ivan-ef/avr-transistor-tester/software/ILI9163.h

/* ************************************************************************
 *
 *   ILI9163 color graphic display controller
 *
 *   (c) 2017-2025 by Markus Reschke
 *
 * ************************************************************************ */


/* ************************************************************************
 *   commands
 * ************************************************************************ */


/*
 *  no operation
 *  - 1 byte cmd
 */

#define CMD_NOP               0b00000000     /* no operation */


/*
 *  software reset
 *  - 1 byte cmd
 */

#define CMD_RESET             0b00000001     /* software reset */


/*
 *  read display identification information
 *  - 1 byte cmd + 4 bytes data (read mode)
 */

#define CMD_READ_DISP_ID      0b00000100     /* read display ID */

/* data byte #1: dummy byte */
/* data byte #2: manufacturer ID (0x54) */
/* data byte #3: module/driver version ID (0x80) */
/* data byte #4: module/driver version ID (0x66) */


/*
 *  read display status
 *  - 1 byte cmd + 5 bytes data (read mode)
 */

#define CMD_READ_STATUS       0b00001001     /* read display status */

/* data byte #1: dummy data */

/* data byte #2: status */
  /* horizontal refresh (horizontal order): */
#define FLAG_STAT_HOR_NORM    0b00000000     /* increment, left to right */
#define FLAG_STAT_HOR_REV     0b00000010     /* decrement, right to left */
  /* RGB/BGR order */
#define FLAG_STAT_COLOR_RGB   0b00000000     /* RGB */
#define FLAG_STAT_COLOR_BGR   0b00000100     /* BGR */
  /* vertical refresh (scan address order): */
#define FLAG_STAT_VER_NORM    0b00000000     /* increment, top to bottom */
#define FLAG_STAT_VER_REV     0b00001000     /* decrement, bottom to top */
  /* row/column exchange: */
#define FLAG_STAT_XY_NORM     0b00000000     /* normal */
#define FLAG_STAT_XY_REV      0b00010000     /* reversed (X & Y swapped) */
  /* column address order: */
#define FLAG_STAT_COL_NORM    0b00000000     /* increment, left to right */
#define FLAG_STAT_COL_REV     0b00100000     /* decrement, right to left */
  /* row address order: */
#define FLAG_STAT_ROW_NORM    0b00000000     /* increment, top to bottom */
#define FLAG_STAT_ROW_REV     0b01000000     /* decrement, bottom to top */
  /* booster voltage: */
#define FLAG_STAT_BOOST_OFF   0b00000000     /* booster on */
#define FLAG_STAT_BOOST_ON    0b10000000     /* booster off */

/* data byte #3: status */
  /* display normal mode: */
#define FLAG_STAT_NORM_OFF    0b00000000     /* off */
#define FLAG_STAT_NORM_ON     0b00000001     /* on */
  /* sleep mode: */
#define FLAG_STAT_SLEEP_OFF   0b00000000     /* off */
#define FLAG_STAT_SLEEP_ON    0b00000010     /* on */
  /* partial mode: */
#define FLAG_STAT_PART_OFF    0b00000000     /* off */
#define FLAG_STAT_PART_ON     0b00000100     /* on */
  /* idle mode: */
#define FLAG_STAT_IDLE_OFF    0b00000000     /* off */
#define FLAG_STAT_IDLE_ON     0b00001000     /* on */
  /* interface color pixel format: */
#define FLAG_STAT_PIX_12      0b00110000     /* 12 bits per pixel */
#define FLAG_STAT_PIX_16      0b01010000     /* 16 bits per pixel */
#define FLAG_STAT_PIX_18      0b01100000     /* 18 bits per pixel */

/* data byte #4: status */
  /* gamma curve - bit 2: bit 0 (always 0) */
  /* tearing effect line: */
#define FLAG_STAT_TEAR_OFF    0b00000000     /* off */
#define FLAG_STAT_TEAR_ON     0b00000010     /* on */
  /* display: */
#define FLAG_STAT_DISP_OFF    0b00000000     /* off */
#define FLAG_STAT_DISP_ON     0b00000100     /* on */
  /* inversion: */
#define FLAG_STAT_INV_OFF     0b00000000     /* off */
#define FLAG_STAT_INV_ON      0b00100000     /* on */
  /* vertical scrolling: */
#define FLAG_STAT_VSCROLL_OFF 0b00000000     /* off */
#define FLAG_STAT_VSCROLL_ON  0b10000000     /* on */

/* data byte #5: status */
  /* tearing effect line mode: */
#define FLAG_STAT_TEAR_MODE1  0b00000000     /* mode 1: V-blanking */
#define FLAG_STAT_TEAR_MODE2  0b00100000     /* mode 2: V-blanking and H-blanking */
  /* gamma curve - bits 1 and 0: */
#define FLAG_STAT_GAMMA1      0b00000000     /* gamma curve 1 */
#define FLAG_STAT_GAMMA2      0b01000000     /* gamma curve 2 */
#define FLAG_STAT_GAMMA3      0b10000000     /* gamma curve 3 */
#define FLAG_STAT_GAMMA4      0b11000000     /* gamma curve 4 */


/*
 *  read display power mode
 *  - 1 byte cmd + 2 bytes data (read mode)
 */

#define CMD_READ_PWR_MODE     0b00001010     /* read display power mode */

/* data byte #1: dummy data */

/* data byte #2: status */
  /* display: */
#define FLAG_DISPLAY_OFF      0b00000000     /* off */
#define FLAG_DISPLAY_ON       0b00000100     /* on */
  /* display normal mode: */
#define FLAG_NORMAL_OFF       0b00000000     /* off (partial display) */
#define FLAG_NORMAL_ON        0b00001000     /* on (normal display) */
  /* sleep mode: */
#define FLAG_SLEEP_OFF        0b00000000     /* off (sleep in) */
#define FLAG_SLEEP_ON         0b00010000     /* on (sleep out) */
  /* partial mode: */
#define FLAG_PARTIAL_OFF      0b00000000     /* off */
#define FLAG_PARTIAL_ON       0b00100000     /* on */
  /* idle mode: */
#define FLAG_IDLE_OFF         0b00000000     /* off */
#define FLAG_IDLE_ON          0b01000000     /* on */
  /* booster voltage: */
#define FLAG_BOOSTER_OFF      0b00000000     /* off */
#define FLAG_BOOSTER_ON       0b10000000     /* on */


/*
 *  read display MADCTL (memory access control)
 *  - 1 byte cmd + 2 bytes data (read mode)
 */

#define CMD_READ_MADCTL       0b00001011     /* read display MADCTL */

/* data byte #1: dummy data */

/* data byte #2: status */
/* same as byte #1 of CMD_MEM_CTRL */
  /* horizontal refreshing direction: */
#define RFLAG_HREFRESH_NORM   0b00000000     /* left to right */
#define RFLAG_HREFRESH_REV    0b00000100     /* right to left */
  /* color order: */
#define RFLAG_COLOR_RGB       0b00000000     /* RGB color filter */
#define RFLAG_COLOR_BGR       0b00001000     /* BGR color filter */
  /* vertical refereshing direction: */
#define RFLAG_VREFRESH_NORM   0b00000000     /* top to bottom */
#define RFLAG_VREFRESH_REV    0b00010000     /* bottom to top */
  /* row/column exchange (MCU to memory): */
#define RFLAG_XY_NORM         0b00000000     /* normal */
#define RFLAG_XY_REV          0b00100000     /* reversed (X & Y swapped) */
  /* column address direction (MCU to memory): */
#define RFLAG_COL_NORM        0b00000000     /* left to right */
#define RFLAG_COL_REV         0b01000000     /* right to left */
  /* row address direction (MCU to memory): */
#define RFLAG_ROW_NORM        0b00000000     /* top to bottom */
#define RFLAG_ROW_REV         0b10000000     /* bottom to top */


/*
 *  read display pixel format
 *  - 1 byte cmd + 2 bytes data (read mode)
 */

#define CMD_READ_PIX_FORMAT   0b00001100     /* read display pixel format */

/* data byte #1: dummy data */

/* data byte #2: status */
/* same as byte #1 of CMD_PIX_FORMAT */
  /* MCU interface color format: */
#define RFLAG_IFPF_12         0b00000011     /* 12 bits per pixel */
#define RFLAG_IFPF_16         0b00000101     /* 16 bits per pixel */
#define RFLAG_IFPF_18         0b00000110     /* 18 bits per pixel */


/*
 *  read display image mode
 *  - 1 byte cmd + 2 bytes data (read mode)
 */

#define CMD_READ_IMG_MODE     0b00001101     /* read display image mode */

/* data byte #1: dummy data */

/* data byte #2: status */
  /* gamma curve */
#define FLAG_IMG_GAMMA1       0b00000000     /* gamma curve 1 */
#define FLAG_IMG_GAMMA2       0b00000001     /* gamma curve 2 */
#define FLAG_IMG_GAMMA3       0b00000010     /* gamma curve 3 */
#define FLAG_IMG_GAMMA4       0b00000011     /* gamma curve 4 */
  /* inversion */
#define FLAG_IMG_INV_OFF      0b00000000     /* off */
#define FLAG_IMG_INV_ON       0b00100000     /* on */
  /* vertical scrolling: */
#define FLAG_IMG_VSCROLL_OFF  0b00000000     /* off */
#define FLAG_IMG_VSCROLL_ON   0b10000000     /* on */


/*
 *  read display signal mode
 *  - 1 byte cmd + 2 bytes data (read mode)
 */

#define CMD_READ_SIG_MODE     0b00001110     /* read display signal mode */

/* data byte #1: dummy data */

/* data byte #2: mode flags */
  /* tearing effect line mode: */
#define FLAG_SIG_TEAR_1       0b00000000     /* mode 1 */
#define FLAG_SIG_TEAR_2       0b01000000     /* mode 2 */
  /* tearing effect line: */
#define FLAG_SIG_TEAR_OFF     0b00000000     /* off */
#define FLAG_SIG_TEAR_ON      0b10000000     /* on */


/*
 *  read peripheral self-diagnostic result
 *  - 1 byte cmd + 2 bytes data (read mode)
 */

#define CMD_READ_SELFDIAG     0b00001111     /* read self-diagnostic result */

/* data byte #1: dummy data */

/* data byte #2: flags */
#define FLAG_SELFDIAG_FUNC    0b01000000     /* functionality detection */
#define FLAG_SELFDIAG_REGLOAD 0b10000000     /* register loading detection */


/*
 *  enter sleep mode (sleep in)
 *  - 1 byte cmd
 *  - requires 5ms delay before sending next command
 *  - requires 120ms delay after CMD_SLEEP_OUT
 */

#define CMD_SLEEP_IN          0b00010000     /* enter sleep mode */


/*
 *  leave sleep mode (sleep out)
 *  - 1 byte cmd
 *  - requires 5ms delay before sending next command
 *  - requires 120ms delay after CMD_SLEEP_IN
 */

#define CMD_SLEEP_OUT         0b00010001     /* leave sleep mode */


/*
 *  enter partial display mode
 *  - 1 byte cmd
 */

#define CMD_PARTIAL_MODE      0b00010010     /* enter partial mode */


/*
 *  enter normal display mode
 *  - 1 byte cmd
 */

#define CMD_NORMAL_MODE       0b00010011     /* normal mode on */


/*
 *  disable display inversion
 *  - 1 byte cmd
 */

#define CMD_INVERSION_OFF     0b00100000     /* display inversion off */


/*
 *  enable display inversion (invert pixels)
 *  - 1 byte cmd
 */

#define CMD_INVERSION_ON      0b00100001     /* display inversion on */


/*
 *  select gamma curve
 *  - 1 byte cmd + 1 byte data
 */

#define CMD_GAMMA_SET         0b00100110     /* gamma set */

/* data byte #1: gamma curve */
#define FLAG_GC_1             0b00000001     /* gamma curve 1 */
#define FLAG_GC_2             0b00000010     /* gamma curve 2 */
#define FLAG_GC_3             0b00000100     /* gamma curve 3 */
#define FLAG_GC_4             0b00001000     /* gamma curve 4 */


/*
 *  disable display output
 *  - 1 byte cmd
 */

#define CMD_DISPLAY_OFF       0b00101000     /* display off */


/*
 *  enable display output
 *  - 1 byte cmd
 */

#define CMD_DISPLAY_ON        0b00101001     /* display on */


/*
 *  set column address (accessible frame area)
 *  - 1 byte cmd + 4 bytes data
 */

#define CMD_COL_ADDR_SET      0b00101010     /* set column address */

/* data byte #1: start column - MSB (bits 15-8) */
/* data byte #2: start column - LSB (bits 7-0) */
/* data byte #3: end column - MSB (bits 15-8) */
/* data byte #4: end column - LSB (bits 7-0) */
/* valid range: 0x0000 - 0x007f/0x007f (128x128) */
/*              0x0000 - 0x007f/0x009f (128x160) */
/*              0x0000 - 0x0083/0x00a1 (132x162) */


/*
 *  set row address (accessible frame area)
 *  - 1 byte cmd + 4 bytes data
 */

#define CMD_ROW_ADDR_SET      0b00101011     /* set row address */

/* data byte #1: start row - MSB (bits 15-8) */
/* data byte #2: start row - LSB (bits 7-0) */
/* data byte #3: end row - MSB (bits 15-8) */
/* data byte #4: end row - LSB (bits 7-0) */
/* valid range: 0x0000 - 0x007f/0x007f (128x128) */
/*              0x0000 - 0x009f/0x007f (128x160) */
/*              0x0000 - 0x00a1/0x0083 (132x162) */


/*
 *  write memory (starting at start column and start row)
 *  - 1 byte cmd + x bytes data
 */

#define CMD_MEM_WRITE         0b00101100     /* write memory */

/* data byte #1 - #x: image data */


/*
 *  color setting for 4k, 65k & 262k
 *  - 1 byte cmd + 128 bytes data
 */

#define CMD_COLOR_LUT         0b00101101     /* set color look up table */

/* data byte #1 - #128: look up table data */


/*
 *  read memory (starting at start column and start row)
 *  - 1 byte cmd + x bytes data (read mode)
 */

#define CMD_MEM_READ          0b00101110     /* read memory */

/* data byte #1: dummy data */
/* data byte #2 - #x: image data */


/*
 *  partial area
 *  - 1 byte cmd + 4 bytes data
 */

#define CMD_PARTIAL_AREA      0b00110000     /* set partial area */

/* data byte #1: start row - MSB (bits 15-8) */
/* data byte #2: start row - LSB (bits 7-0) */
/* data byte #3: end row - MSB (bits 15-8) */
/* data byte #4: end row - LSB (bits 7-0) */
/* valid range: 0x0000 - 0x09f/0x00a1 */


/*
 *  vertical scrolling definition (scrolling area)
 *  - 1 byte cmd + 6 bytes data
 */

#define CMD_VSCROLL_AREA      0b00110011     /* set v-scroll area */

/* data byte #1: top fixed area - MSB (bits 15-8) */
/* data byte #2: top fixed area - LSB (bits 7-0) */
/* data byte #3: vertical scrolling area - MSB (bits 15-8) */
/* data byte #4: vertical scrolling area - LSB (bits 7-0) */
/* data byte #5: bottom fixed area - MSB (bits 15-8) */
/* data byte #6: bottom fixed area - LSB (bits 7-0) */


/*
 *  disable tearing effect line
 *  - 1 byte cmd
 */

#define CMD_TEAR_OFF          0b00110100     /* disable tearing effect */


/*
 *  enable tearing effect line
 *  - 1 byte cmd + 1 byte data
 */

#define CMD_TEAR_ON           0b00110101     /* enable tearing effect */

/* data byte #1: mode */
  /* tearing effect mode: */
#define FLAG_TEAR_MODE_0      0b00000000     /* V-blanking only */
#define FLAG_TEAR_MODE_1      0b00000001     /* V-blanking and H-blanking */


/*
 *  memory access control
 *  - 1 byte cmd + 1 byte data
 */

#define CMD_MEM_CTRL          0b00110110     /* memory access control */

/* data byte #1: read/write scanning direction of frame memory */
/* same as byte #2 of CMD_READ_MADCTL */
  /* horizontal refreshing direction: */
#define FLAG_HREFRESH_NORM    0b00000000     /* left to right */
#define FLAG_HREFRESH_REV     0b00000100     /* right to left */
  /* color order: */
#define FLAG_COLOR_RGB        0b00000000     /* RGB color filter */
#define FLAG_COLOR_BGR        0b00001000     /* BGR color filter */
  /* vertical refereshing direction: */
#define FLAG_VREFRESH_NORM    0b00000000     /* top to bottom */
#define FLAG_VREFRESH_REV     0b00010000     /* bottom to top */
  /* row/column exchange (MCU to memory): */
#define FLAG_XY_NORM          0b00000000     /* normal */
#define FLAG_XY_REV           0b00100000     /* reversed (X & Y swapped) */
  /* column address direction (MCU to memory): */
#define FLAG_COL_NORM         0b00000000     /* left to right */
#define FLAG_COL_REV          0b01000000     /* right to left */
  /* row address direction (MCU to memory): */
#define FLAG_ROW_NORM         0b00000000     /* top to bottom */
#define FLAG_ROW_REV          0b10000000     /* bottom to top */


/*
 *  vertical scrolling start address
 *  - 1 byte cmd + 2 bytes data
 */

#define CMD_VSCROLL_START     0b00110111     /* set v-scroll start */

/* data byte #1: start row - MSB (bits 15-8) */
/* data byte #2: start row - LSB (bits 7-0) */


/*
 *  leave idle mode (full color depth)
 *  - 1 byte cmd
 */

#define CMD_IDLE_OFF          0b00111000     /* disable idle mode */


/*
 *  enter idle mode (8bit color depth)
 *  - 1 byte cmd
 */

#define CMD_IDLE_ON           0b00111001     /* enable idle mode */


/*
 *  set pixel format for RGB image data
 *  - 1 byte cmd + 1 byte data
 */

#define CMD_PIX_FORMAT        0b00111010     /* set pixel format */

/* data byte #1: formats */
/* same as byte #2 of CMD_READ_PIX_FORMAT */
  /* MCU interface color format: */
#define FLAG_IFPF_12          0b00000011     /* 12 bits per pixel */
#define FLAG_IFPF_16          0b00000101     /* 16 bits per pixel */
#define FLAG_IFPF_18          0b00000110     /* 18 bits per pixel */


/*
 *  read ID1
 *  - 1 byte cmd + 2 bytes data (read mode)
 */

#define CMD_READ_ID1          0b11011010     /* read ID1 (manufacturer) */

/* data byte #1: dummy data */
/* data byte #2: LCD module manufacturer ID */


/*
 *  read ID2
 *  - 1 byte cmd + 2 bytes data (read mode)
 */

#define CMD_READ_ID2          0b11011011     /* read ID2 (driver version) */

/* data byte #1: dummy data */
/* data byte #2: LCD module/driver version */


/*
 *  read ID3
 *  - 1 byte cmd + 2 bytes data (read mode)
 */

#define CMD_READ_ID3          0b11011100     /* read ID3 (driver) */

/* data byte #1: dummy data */
/* data byte #2: LCD module/driver ID */


/*
 *  frame rate control in normal mode (full color)
 *  - 1 byte cmd + 2 bytes data
 */

#define CMD_FRAME_CTRL_NORM   0b10110001     /* frame control in normal mode */

/* data byte #1: division ratio for internal clock */
  /* valid range: 0 - 15 */

/* data byte #2: v-sync porch for internal clock */
  /* valid range: 0 - 63 */


/*
 *  frame rate control in idle mode (8bit color depth)
 *  - 1 byte cmd + 2 bytes data
 */

#define CMD_FRAME_CTRL_IDLE   0b10110010     /* frame control in idle mode */

/* data byte #1: division ratio for internal clock */
  /* valid range: 0 - 15 */

/* data byte #2: v-sync porch for internal clock */
  /* valid range: 0 - 63 */


/*
 *  frame rate control in partial mode (full color)
 *  - 1 byte cmd + 2 bytes data
 */

#define CMD_FRAME_CTRL_PART   0b10110011     /* frame control in partial mode */

/* data byte #1: division ratio for internal clock */
  /* valid range: 0 - 15 */

/* data byte #2: v-sync porch for internal clock */
  /* valid range: 0 - 63 */



/*
 *  display inversion control
 *  - 1 byte cmd + 1 byte data
 */

#define CMD_INVERS_CTRL       0b10110100     /* display inversion control */

/* data byte #1: mode switches */
  /* for full color partial mode: */
#define FLAG_NLC_LINE         0b00000000     /* line inversion */
#define FLAG_NLC_FRAME        0b00000001     /* frame inversion */
  /* for idle mode: */
#define FLAG_NLB_LINE         0b00000000     /* line inversion */
#define FLAG_NLB_FRAME        0b00000010     /* frame inversion */
  /* for full color normal mode: */
#define FLAG_NLA_LINE         0b00000000     /* line inversion */
#define FLAG_NLA_FRAME        0b00000100     /* frame inversion */


/*
 *  source driver direction control
 *  - 1 byte cmd + 1 byte data
 */

#define CMD_SOURCE_DRV        0b10110111     /* set source driver direction */

/* data byte #1: soure output direction select register */
#define FLAG_SOURCE_DRV_NORM  0b00000000     /* normal */
#define FLAG_SOURCE_DRV_REV   0b00000001     /* reversed */


/*
 *  gate driver direction control
 *  - 1 byte cmd + 1 byte data
 */

#define CMD_GATE_DRV          0b10111000     /* set gate driver direction */

/* data byte #1: source output direction select register */
#define FLAG_GATEE_DRV_NORM   0b00000000     /* normal */
#define FLAG_GATEE_DRV_REV    0b00000001     /* reversed */


/*
 *  power control 1
 *  - 1 byte cmd + 2 bytes data
 */

#define CMD_POWER_CTRL_1      0b11000000     /* power control 1 */

/* data byte #1: GVDD level (reference for VCOM) */
#define FLAG_VRH_500          0b00000000     /* 5.00V */
#define FLAG_VRH_475          0b00000001     /* 4.75V */
#define FLAG_VRH_470          0b00000010     /* 4.70V */
#define FLAG_VRH_465          0b00000011     /* 4.65V */
#define FLAG_VRH_460          0b00000100     /* 4.60V */
#define FLAG_VRH_455          0b00000101     /* 4.55V */
#define FLAG_VRH_450          0b00000110     /* 4.50V */
#define FLAG_VRH_445          0b00000111     /* 4.45V */
#define FLAG_VRH_440          0b00001000     /* 4.40V */
#define FLAG_VRH_435          0b00001001     /* 4.35V */
#define FLAG_VRH_430          0b00001010     /* 4.30V */
#define FLAG_VRH_425          0b00001011     /* 4.25V */
#define FLAG_VRH_420          0b00001100     /* 4.20V */
#define FLAG_VRH_415          0b00001101     /* 4.15V */
#define FLAG_VRH_410          0b00001110     /* 4.10V */
#define FLAG_VRH_405          0b00001111     /* 4.05V */
#define FLAG_VRH_400          0b00010000     /* 4.00V */
#define FLAG_VRH_395          0b00010001     /* 3.95V */
#define FLAG_VRH_390          0b00010010     /* 3.90V */
#define FLAG_VRH_385          0b00010011     /* 3.85V */
#define FLAG_VRH_380          0b00010100     /* 3.80V */
#define FLAG_VRH_375          0b00010101     /* 3.75V */
#define FLAG_VRH_370          0b00010110     /* 3.70V */
#define FLAG_VRH_365          0b00010111     /* 3.65V */
#define FLAG_VRH_360          0b00011000     /* 3.60V */
#define FLAG_VRH_355          0b00011001     /* 3.55V */
#define FLAG_VRH_350          0b00011010     /* 3.50V */
#define FLAG_VRH_345          0b00011011     /* 3.45V */
#define FLAG_VRH_340          0b00011100     /* 3.40V */
#define FLAG_VRH_335          0b00011101     /* 3.35V */
#define FLAG_VRH_325          0b00011110     /* 3.25V */
#define FLAG_VRH_300          0b00011111     /* 3.00V */

/* data byte #2: VCI 1 */
#define FLAG_VCI_275          0b00000000     /* 2.75V */
#define FLAG_VCI_270          0b00000001     /* 2.70V */
#define FLAG_VCI_265          0b00000010     /* 2.65V */
#define FLAG_VCI_260          0b00000011     /* 2.60V */
#define FLAG_VCI_255          0b00000100     /* 2.55V */
#define FLAG_VCI_250          0b00000101     /* 2.50V */
#define FLAG_VCI_245          0b00000110     /* 2.45V */
#define FLAG_VCI_240          0b00000111     /* 2.40V */


/*
 *  power control 2
 *  - 1 byte cmd + 1 byte data
 */

#define CMD_POWER_CTRL_2      0b11000001     /* power control 2 */

/* data byte #1: VGH and VGL factors for step-up converter */
                                             /* VGH / VGL */
#define FLAG_BT_0             0b00000000     /* 4* (9.8)   / -3* (-7.35) */
#define FLAG_BT_1             0b00000001     /* 4* (9.8)   / -4* (-9.8) */
#define FLAG_BT_2             0b00000010     /* 5* (12.25) / -3* (-7.35) */
#define FLAG_BT_3             0b00000011     /* 5* (12.25) / -4* (-9.8) */
#define FLAG_BT_4             0b00000100     /* 5* (12.25) / -5* (-12.25) */
#define FLAG_BT_5             0b00000101     /* 6* (14.7)  / -3* (-7.35) */
#define FLAG_BT_6             0b00000101     /* 6* (14.7)  / -4* (-9.8) */
#define FLAG_BT_7             0b00000111     /* 6* (14.7)  / -5* (-12.25) */


/*
 *  power control 3 (normal mode / full color)
 *  - 1 byte cmd + 2 bytes data
 */

#define CMD_POWER_CTRL_3      0b11000010     /* power control 3 */

/* data byte #1: current for source driver OPamp */
#define FLAG_APA_0            0b00000000     /* least */
#define FLAG_APA_1            0b00000001     /* small */
#define FLAG_APA_2            0b00000010     /* medium low */
#define FLAG_APA_3            0b00000011     /* medium */
#define FLAG_APA_4            0b00000100     /* medium high */
#define FLAG_APA_5            0b00000101     /* large */
#define FLAG_APA_6            0b00000110     /* reserved */
#define FLAG_APA_7            0b00000111     /* reserved */

/* data byte #2: step-up cycles of booster circuit */
                                             /* circuit 1 / circuits 2 & 3 */
#define FLAG_DCA_0            0b00000000     /* BCLK/1 / BCLK/4 */
#define FLAG_DCA_1            0b00000001     /* BCLK/1 / BCLK/8 */
#define FLAG_DCA_2            0b00000010     /* BCLK/1 / BCLK/8 */
#define FLAG_DCA_3            0b00000011     /* BCLK/2 / BCLK/16 */
#define FLAG_DCA_4            0b00000100     /* BCLK/2 / BCLK/16 */
#define FLAG_DCA_5            0b00000101     /* BCLK/4 / BCLK/32 */
#define FLAG_DCA_6            0b00000110     /* BCLK/4 / BCLK/64 */
#define FLAG_DCA_7            0b00000111     /* BCLK/8 / BCLK/64 */


/*
 *  power control 4 (idle mode / 8bit color)
 *  - 1 byte cmd + 2 bytes data
 */

#define CMD_POWER_CTRL_4      0b11000011     /* power control 4 */

/* data byte #1: current for source driver OPamp */
#define FLAG_APB_0            0b00000000     /* least */
#define FLAG_APB_1            0b00000001     /* small */
#define FLAG_APB_2            0b00000010     /* medium low */
#define FLAG_APB_3            0b00000011     /* medium */
#define FLAG_APB_4            0b00000100     /* medium high */
#define FLAG_APB_5            0b00000101     /* large */
#define FLAG_APB_6            0b00000110     /* reserved */
#define FLAG_APB_7            0b00000111     /* reserved */

/* data byte #2: step-up cycles of booster circuit */
                                             /* circuit 1 / circuits 2 & 3 */
#define FLAG_DCB_0            0b00000000     /* BCLK/1 / BCLK/4 */
#define FLAG_DCB_1            0b00000001     /* BCLK/1 / BCLK/8 */
#define FLAG_DCB_2            0b00000010     /* BCLK/1 / BCLK/8 */
#define FLAG_DCB_3            0b00000011     /* BCLK/2 / BCLK/16 */
#define FLAG_DCB_4            0b00000100     /* BCLK/2 / BCLK/16 */
#define FLAG_DCB_5            0b00000101     /* BCLK/4 / BCLK/32 */
#define FLAG_DCB_6            0b00000110     /* BCLK/4 / BCLK/64 */
#define FLAG_DCB_7            0b00000111     /* BCLK/8 / BCLK/64 */


/*
 *  power control 5 (partial mode / full color)
 *  - 1 byte cmd + 2 bytes data
 */

#define CMD_POWER_CTRL_5      0b11000100     /* power control 5 */

/* data byte #1: current for source driver OPamp */
#define FLAG_APC_0            0b00000000     /* least */
#define FLAG_APC_1            0b00000001     /* small */
#define FLAG_APC_2            0b00000010     /* medium low */
#define FLAG_APC_3            0b00000011     /* medium */
#define FLAG_APC_4            0b00000100     /* medium high */
#define FLAG_APC_5            0b00000101     /* large */
#define FLAG_APC_6            0b00000110     /* reserved */
#define FLAG_APC_7            0b00000111     /* reserved */

/* data byte #2: step-up cycles of booster circuit */
                                             /* circuit 1 / circuits 2 & 3 */
#define FLAG_DCC_0            0b00000000     /* BCLK/1 / BCLK/4 */
#define FLAG_DCC_1            0b00000001     /* BCLK/1 / BCLK/8 */
#define FLAG_DCC_2            0b00000010     /* BCLK/1 / BCLK/8 */
#define FLAG_DCC_3            0b00000011     /* BCLK/2 / BCLK/16 */
#define FLAG_DCC_4            0b00000100     /* BCLK/2 / BCLK/16 */
#define FLAG_DCC_5            0b00000101     /* BCLK/4 / BCLK/32 */
#define FLAG_DCC_6            0b00000110     /* BCLK/4 / BCLK/64 */
#define FLAG_DCC_7            0b00000111     /* BCLK/8 / BCLK/64 */


/*
 *  VCOM control 1
 *  - 1 byte cmd + 2 bytes data
 */

#define CMD_VCOM_CTRL_1       0b11000101     /* VCOM control 1 */

/* data byte #1: VCOMH voltage */
#define FLAG_VMH_MIN          0b00000000     /* minumum value */
#define FLAG_VMH_2500         0b00000000     /* 2.500V */
#define FLAG_VMH_2525         0b00000001     /* 2.525V */
#define FLAG_VMH_2550         0b00000010     /* 2.550V */
#define FLAG_VMH_2575         0b00000011     /* 2.575V */
#define FLAG_VMH_2600         0b00000100     /* 2.600V */
#define FLAG_VMH_2625         0b00000101     /* 2.625V */
#define FLAG_VMH_2650         0b00000110     /* 2.650V */
#define FLAG_VMH_2675         0b00000111     /* 2.675V */
#define FLAG_VMH_2700         0b00001000     /* 2.700V */
#define FLAG_VMH_2725         0b00001001     /* 2.725V */
#define FLAG_VMH_2750         0b00001010     /* 2.750V */
#define FLAG_VMH_2775         0b00001011     /* 2.775V */
#define FLAG_VMH_2800         0b00001100     /* 2.800V */
#define FLAG_VMH_2825         0b00001101     /* 2.825V */
#define FLAG_VMH_2850         0b00001110     /* 2.850V */
#define FLAG_VMH_2875         0b00001111     /* 2.875V */
#define FLAG_VMH_2900         0b00010000     /* 2.900V */
#define FLAG_VMH_2925         0b00010001     /* 2.925V */
#define FLAG_VMH_2950         0b00010010     /* 2.950V */
#define FLAG_VMH_2975         0b00010011     /* 2.975V */
#define FLAG_VMH_3000         0b00010100     /* 3.000V */
#define FLAG_VMH_3025         0b00010101     /* 3.025V */
#define FLAG_VMH_3050         0b00010110     /* 3.050V */
#define FLAG_VMH_3075         0b00010111     /* 3.075V */
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
#define FLAG_VML_0175         0b01011101     /* -0.175V */
#define FLAG_VML_0150         0b01011110     /* -0.150V */
#define FLAG_VML_0125         0b01011111     /* -0.125V */
#define FLAG_VML_0100         0b01100000     /* -0.100V */
#define FLAG_VML_0075         0b01100001     /* -0.075V */
#define FLAG_VML_0050         0b01100010     /* -0.050V */
#define FLAG_VML_0025         0b01100011     /* -0.025V */
#define FLAG_VML_0000         0b01100100     /* 0.000V */
#define FLAG_VML_MAX          0b01100100     /* maximum value */


/*
 *  VCOM control 2
 *  - 1 byte cmd + 1 byte data
 */

#define CMD_VCOM_CTRL_2       0b11000110     /* VCOM control 2 */

/* data byte #1: VCOMAC voltage */
 /* range: 0 - 31 */


/*
 *  VCOM offset control
 *  - 1 byte cmd + 1 byte data
 */

#define CMD_VCOM_OFFSET       0b11000111     /* VCOM offset control */

/* data byte #1: */
 /* VCOMH voltage */
                                             /* VMH / VML */
#define FLAG_VMF_MIN          0b00000000     /* minumum value */
#define FLAG_VMF_M64          0b00000000     /* -0 */
#define FLAG_VMF_M63          0b00000001     /* -63d */
#define FLAG_VMF_M62          0b00000010     /* -62d */
#define FLAG_VMF_M61          0b00000011     /* -61d */
#define FLAG_VMF_M60          0b00000100     /* -60d */
#define FLAG_VMF_M59          0b00000101     /* -59d */
#define FLAG_VMF_M58          0b00000110     /* -58d */
#define FLAG_VMF_M57          0b00000111     /* -57d */
#define FLAG_VMF_M56          0b00001000     /* -56d */
#define FLAG_VMF_M55          0b00001001     /* -55d */
#define FLAG_VMF_M54          0b00001010     /* -54d */
#define FLAG_VMF_M53          0b00001011     /* -53d */
#define FLAG_VMF_M52          0b00001100     /* -52d */
#define FLAG_VMF_M51          0b00001101     /* -51d */
#define FLAG_VMF_M50          0b00001110     /* -50d */
#define FLAG_VMF_M49          0b00001111     /* -49d */
#define FLAG_VMF_M48          0b00010000     /* -48d */
#define FLAG_VMF_M47          0b00010001     /* -47d */
#define FLAG_VMF_M46          0b00010010     /* -46d */
#define FLAG_VMF_M45          0b00010011     /* -45d */
#define FLAG_VMF_M44          0b00010100     /* -44d */
#define FLAG_VMF_M43          0b00010101     /* -43d */
#define FLAG_VMF_M42          0b00010110     /* -42d */
#define FLAG_VMF_M41          0b00010111     /* -41d */
#define FLAG_VMF_M40          0b00011000     /* -40d */
#define FLAG_VMF_M39          0b00011001     /* -39d */
#define FLAG_VMF_M38          0b00011010     /* -38d */
#define FLAG_VMF_M37          0b00011011     /* -37d */
#define FLAG_VMF_M36          0b00011100     /* -36d */
#define FLAG_VMF_M35          0b00011101     /* -35d */
#define FLAG_VMF_M34          0b00011110     /* -34d */
#define FLAG_VMF_M33          0b00011111     /* -33d */
#define FLAG_VMF_M32          0b00100000     /* -32d */
#define FLAG_VMF_M31          0b00100001     /* -31d */
#define FLAG_VMF_M30          0b00100010     /* -30d */
#define FLAG_VMF_M29          0b00100011     /* -29d */
#define FLAG_VMF_M28          0b00100100     /* -28d */
#define FLAG_VMF_M27          0b00100101     /* -27d */
#define FLAG_VMF_M26          0b00100110     /* -26d */
#define FLAG_VMF_M25          0b00100111     /* -25d */
#define FLAG_VMF_M24          0b00101000     /* -24d */
#define FLAG_VMF_M23          0b00101001     /* -23d */
#define FLAG_VMF_M22          0b00101010     /* -22d */
#define FLAG_VMF_M21          0b00101011     /* -21d */
#define FLAG_VMF_M20          0b00101100     /* -20d */
#define FLAG_VMF_M19          0b00101101     /* -19d */
#define FLAG_VMF_M18          0b00101110     /* -18d */
#define FLAG_VMF_M17          0b00101111     /* -17d */
#define FLAG_VMF_M16          0b00110000     /* -16d */
#define FLAG_VMF_M15          0b00110001     /* -15d */
#define FLAG_VMF_M14          0b00110010     /* -14d */
#define FLAG_VMF_M13          0b00110011     /* -13d */
#define FLAG_VMF_M12          0b00110100     /* -12d */
#define FLAG_VMF_M11          0b00110101     /* -11d */
#define FLAG_VMF_M10          0b00110110     /* -10d */
#define FLAG_VMF_M09          0b00110111     /* -9d */
#define FLAG_VMF_M08          0b00111000     /* -8d */
#define FLAG_VMF_M07          0b00111001     /* -7d */
#define FLAG_VMF_M06          0b00111010     /* -6d */
#define FLAG_VMF_M05          0b00111011     /* -5d */
#define FLAG_VMF_M04          0b00111100     /* -4d */
#define FLAG_VMF_M03          0b00111101     /* -3d */
#define FLAG_VMF_M02          0b00111110     /* -2d */
#define FLAG_VMF_M01          0b00111111     /* -1d */
#define FLAG_VMF_M00          0b01000000     /* -0 */
#define FLAG_VMF_P00          0b01000000     /* +0 */
#define FLAG_VMF_P01          0b01000001     /* +1d */
#define FLAG_VMF_P02          0b01000010     /* +2d */
#define FLAG_VMF_P03          0b01000011     /* +3d */
#define FLAG_VMF_P04          0b01000100     /* +4d */
#define FLAG_VMF_P05          0b01000101     /* +5d */
#define FLAG_VMF_P06          0b01000110     /* +6d */
#define FLAG_VMF_P07          0b01000111     /* +7d */
#define FLAG_VMF_P08          0b01001000     /* +8d */
#define FLAG_VMF_P09          0b01001001     /* +9d */
#define FLAG_VMF_P10          0b01001010     /* +10d */
#define FLAG_VMF_P11          0b01001011     /* +11d */
#define FLAG_VMF_P12          0b01001100     /* +12d */
#define FLAG_VMF_P13          0b01001101     /* +13d */
#define FLAG_VMF_P14          0b01001110     /* +14d */
#define FLAG_VMF_P15          0b01001111     /* +15d */
#define FLAG_VMF_P16          0b01010000     /* +16d */
#define FLAG_VMF_P17          0b01010001     /* +17d */
#define FLAG_VMF_P18          0b01010010     /* +18d */
#define FLAG_VMF_P19          0b01010011     /* +19d */
#define FLAG_VMF_P20          0b01010100     /* +20d */
#define FLAG_VMF_P21          0b01010101     /* +21d */
#define FLAG_VMF_P22          0b01010110     /* +22d */
#define FLAG_VMF_P23          0b01010111     /* +23d */
#define FLAG_VMF_P24          0b01011000     /* +24d */
#define FLAG_VMF_P25          0b01011001     /* +25d */
#define FLAG_VMF_P26          0b01011010     /* +26d */
#define FLAG_VMF_P27          0b01011011     /* +27d */
#define FLAG_VMF_P28          0b01011100     /* +28d */
#define FLAG_VMF_P29          0b01011101     /* +29d */
#define FLAG_VMF_P30          0b01011110     /* +30d */
#define FLAG_VMF_P31          0b01011111     /* +31d */
#define FLAG_VMF_P32          0b01100000     /* +32d */
#define FLAG_VMF_P33          0b01100001     /* +33d */
#define FLAG_VMF_P34          0b01100010     /* +34d */
#define FLAG_VMF_P35          0b01100011     /* +35d */
#define FLAG_VMF_P36          0b01100100     /* +36d */
#define FLAG_VMF_P37          0b01100101     /* +37d */
#define FLAG_VMF_P38          0b01100110     /* +38d */
#define FLAG_VMF_P39          0b01100111     /* +39d */
#define FLAG_VMF_P40          0b01101000     /* +40d */
#define FLAG_VMF_P41          0b01101001     /* +41d */
#define FLAG_VMF_P42          0b01101010     /* +42d */
#define FLAG_VMF_P43          0b01101011     /* +43d */
#define FLAG_VMF_P44          0b01101100     /* +44d */
#define FLAG_VMF_P45          0b01101101     /* +45d */
#define FLAG_VMF_P46          0b01101110     /* +46d */
#define FLAG_VMF_P47          0b01101111     /* +47d */
#define FLAG_VMF_P48          0b01110000     /* +48d */
#define FLAG_VMF_P49          0b01110001     /* +49d */
#define FLAG_VMF_P50          0b01110010     /* +50d */
#define FLAG_VMF_P51          0b01110011     /* +51d */
#define FLAG_VMF_P52          0b01110100     /* +52d */
#define FLAG_VMF_P53          0b01110101     /* +53d */
#define FLAG_VMF_P54          0b01110110     /* +54d */
#define FLAG_VMF_P55          0b01110111     /* +55d */
#define FLAG_VMF_P56          0b01111000     /* +56d */
#define FLAG_VMF_P57          0b01111001     /* +57d */
#define FLAG_VMF_P58          0b01111010     /* +58d */
#define FLAG_VMF_P59          0b01111011     /* +59d */
#define FLAG_VMF_P60          0b01111100     /* +60d */
#define FLAG_VMF_P61          0b01111101     /* +6d */
#define FLAG_VMF_P62          0b01111110     /* +6d */
#define FLAG_VMF_P63          0b01111111     /* +63d */
#define FLAG_VMF_MAX          0b01111111     /* maximum value */
 /* select VMF value */
#define FLAG_VMF_NV           0b00000000     /* from NV memory */
#define FLAG_VMF_REG          0b10000000     /* from register */


/*
 *  write ID4 value to EEPROM
 *  - 1 byte cmd + 5 bytes data
 */

#define CMD_WRITE_ID4         0b11010011     /* write ID4 */

/* data byte #1: dummy byte */
/* data byte #2: driver IC ID (8 bits) */
/* data byte #3: driver IC part number ID (8 bits) */
/* data byte #4: driver IC version ID (4 bits) */
/* data byte #5: dummy byte */


/*
 *  NV memory function controller
 *  - 1 byte cmd + 3 bytes data
 */

#define CMD_NV_CTRL1          0b11011010     /* NV memory function controller */
// or 0x7d = 0b11010111?

/* data byte #1: fixed value */
#define FLAG_NV_CTRL1_1       0b01010101     /* fixed value 0x55 */

/* data byte #2: fixed value */
#define FLAG_NV_CTRL1_2       0b10101010     /* fixed value 0xaa */

/* data byte #3: fixed value */
#define FLAG_NV_CTRL1_3       0b01100110     /* fixed value 0x66 */


/*
 *  NV memory function controller 2
 *  - 1 byte cmd + 3 bytes data
 */

#define CMD_NV_CTRL2          0b11011010     /* NV memory function controller 2 */
// or 0xde = 0b11011110?

/* data byte #1: fixed value */
#define FLAG_NV_CTRL2_1       0b01010101     /* fixed value 0x55 */

/* data byte #2: fixed value */
#define FLAG_NV_CTRL2_2       0b10101010     /* fixed value 0xaa */

/* data byte #3: fixed value */
#define FLAG_NV_CTRL2_3       0b01100110     /* fixed value 0x66 */


/*
 *  positive gamma correction, gray scale voltage
 *  - 1 byte cmd + 15 bytes data
 */

#define CMD_GAMMA_CORR_POS    0b11100000     /* positive gamma correction */

/* data bytes: please see datasheet */


/*
 *  negative gamma correction, gray scale voltage
 *  - 1 byte cmd + 15 bytes data
 */

#define CMD_GAMMA_CORR_NEG    0b11100001     /* negative gamma correction */

/* data bytes: please see datasheet */


/*
 *  gamma adjustment control
 *  - 1 byte cmd + 1 byte data
 */

#define CMD_GAMMA_SELECT      0b11110010     /* gamma adjustment control */

/* data byte #1: control */
#define FLAG_GAMMA_OFF        0b00000000     /* disable (default) */
#define FLAG_GAMMA_ON         0b00000001     /* enable */



/* ************************************************************************
 *   EOF
 * ************************************************************************ */
